TinkerTavern/RFID-Door-Locking/Development/data/Test2.jpg

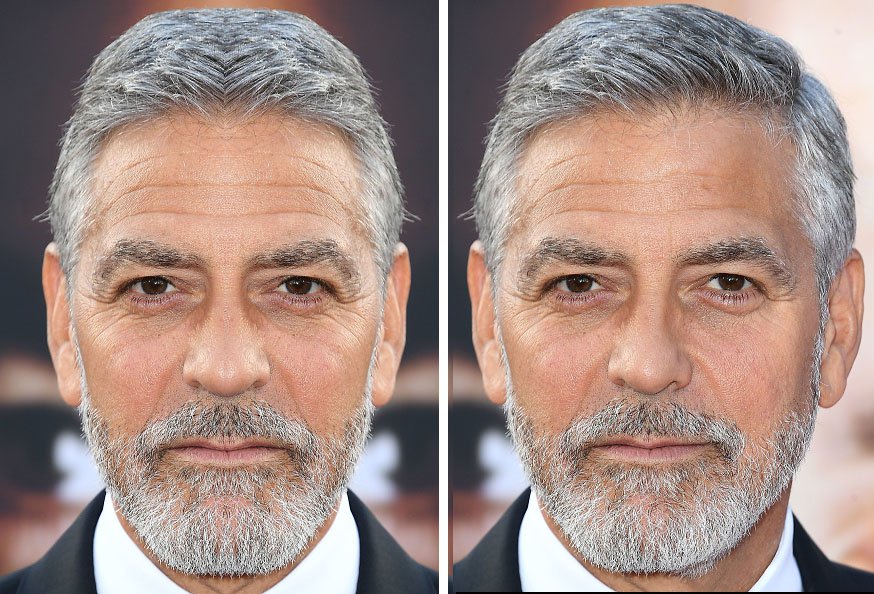
Development/data/Test2.jpg
