TinkerTavern/RFID-Door-Locking/Development/data/test1.jpg

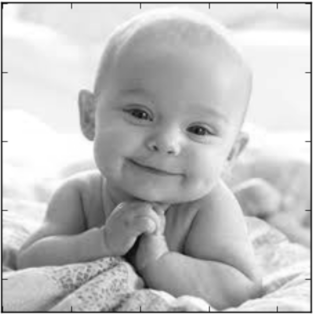
Development/data/test1.jpg
