TinkerTavern/RFID-Door-Locking/Development/OpenCV Tutorial.py

import cv2 as cv
import numpy as np
import time


def toRGB(img):
    return cv.cvtColor(img, cv.COLOR_BGR2RGB)

def toGray(img):
    return cv.cvtColor(img, cv.COLOR_BGR2GRAY)

#load cascade classifier training file for haarcascade 
face_cascade = cv.CascadeClassifier('data/haarcascade_frontalface_alt.xml')
eye_cascade = cv.CascadeClassifier('data/haarcascade_eye.xml')

img = cv.imread("data/test2.jpg")
gray = toGray(img)

faces = face_cascade.detectMultiScale(gray, 1.3, 5)
for (x,y,w,h) in faces:
    cv.rectangle(img,(x,y),(x+w,y+h),(255,0,0),2)
    roi_gray = gray[y:y+h, x:x+w]
    roi_color = img[y:y+h, x:x+w]
    eyes = eye_cascade.detectMultiScale(roi_gray)
    for (ex,ey,ew,eh) in eyes:
        cv.rectangle(roi_color,(ex,ey),(ex+ew,ey+eh),(0,255,0),2)

cv.imshow('img',img)
cv.waitKey(0)
cv.destroyAllWindows()
